stevenchadburrow/Neon6502/Neo6502-Simulator.c

// Neo6502-Simulator.c

// To compile:  gcc -o Neo6502-Simulator.o Neo6502-Simulator.c -lglfw -lGL

// Simulates code for the Neo6502

#include <stdio.h>
#include <stdlib.h>
#include <time.h>

// uses OpenGL for graphics and keyboard
#include <GLFW/glfw3.h>
#include <GL/gl.h>

GLFWwindow* window;
int opengl_window_x = 640;
int opengl_window_y = 480;
int opengl_keyboard_state[512];


unsigned char mandelbrot[80*240] = {

0x55, 0x55, 0x55, 0x55, 0x55, 0x55, 0x55, 0x55, 0x55, 0x55, 0x55, 0x55, 0x55, 0x7F, 0xFE, 0xB2, 
0xA1, 0x55, 0xD5, 0x55, 0x15, 0x29, 0x1C, 0xAA, 0xA0, 0x08, 0xAA, 0xAA, 0xA0, 0x52, 0xA2, 0xAA, 
0x20, 0x28, 0xFF, 0xFF, 0xFF, 0xFF, 0xFF, 0xE2, 0xF0, 0xA0, 0x55, 0x55, 0x55, 0x54, 0x0A, 0xAA, 
0x2A, 0xAA, 0x0A, 0xAA, 0xAA, 0xAA, 0xA8, 0x0A, 0x1A, 0x2A, 0xFC, 0xF5, 0x55, 0x55, 0x55, 0x55, 
0x55, 0x55, 0x55, 0x55, 0x55, 0x55, 0x55, 0x55, 0x55, 0x55, 0x55, 0x55, 0x55, 0x55, 0x55, 0x55, 

0x55, 0x55, 0x55, 0x55, 0x55, 0x55, 0x55, 0x55, 0x55, 0x55, 0x55, 0x55, 0x55, 0x7F, 0xFC, 0xA2, 
0x85, 0x5F, 0xFD, 0x55, 0x42, 0x88, 0x16, 0xAA, 0xAA, 0xA8, 0x2A, 0xA2, 0x21, 0x54, 0xA2, 0xAA, 
0xA8, 0x2A, 0xBF, 0xFF, 0xFF, 0xFF, 0xFF, 0xFE, 0xE2, 0x80, 0x55, 0x55, 0x55, 0x42, 0x8A, 0xAA, 
0xEA, 0xAA, 0x8A, 0xAA, 0xAA, 0xA2, 0xA0, 0x6A, 0x2A, 0x2F, 0xC8, 0xF5, 0x55, 0x55, 0x55, 0x55, 
0x55, 0x55, 0x55, 0x55, 0x55, 0x55, 0x55, 0x55, 0x55, 0x55, 0x55, 0x55, 0x55, 0x55, 0x55, 0x55, 

0x55, 0x55, 0x55, 0x55, 0x55, 0x55, 0x55, 0x55, 0x55, 0x55, 0x55, 0x55, 0x55, 0x7F, 0x3E, 0xA8, 
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
0x80, 0x55, 0x55, 0x55, 0x44, 0x8A, 0xA2, 0xFF, 0xFF, 0xFF, 0xFF, 0xFF, 0xFF, 0xFB, 0xEA, 0xAA, 
0x0A, 0x0F, 0x87, 0xD2, 0xA4, 0x88, 0xAA, 0xAA, 0xAA, 0xAA, 0x00, 0xAA, 0x15, 0x55, 0x7E, 0x2D, 
0x54, 0x0A, 0xBF, 0xAF, 0x55, 0x55, 0x55, 0x55, 0x55, 0x55, 0x55, 0x55, 0x55, 0x55, 0x55, 0x55, 

0x55, 0x55, 0x55, 0x55, 0x55, 0x55, 0x55, 0x55, 0x55, 0x55, 0x55, 0x55, 0x55, 0x55, 0x55, 0x55, 
0x55, 0x5F, 0xAE, 0xBE, 0xAA, 0x88, 0x40, 0xA0, 0x8A, 0xAA, 0xAA, 0x2F, 0xAA, 0xA4, 0x82, 0xA8, 
0xA4, 0x55, 0x55, 0x55, 0x50, 0x0A, 0x8E, 0xBF, 0xFF, 0xFF, 0xFF, 0xFF, 0xFF, 0xFA, 0x8A, 0x22, 
0xAA, 0xAA, 0x87, 0x50, 0xA8, 0x88, 0x2A, 0xAA, 0xAA, 0xAA, 0x80, 0x02, 0x95, 0x55, 0x7F, 0xBD, 
0x54, 0xAA, 0xA3, 0xFB, 0xD5, 0x55, 0x55, 0x55, 0x55, 0x55, 0x55, 0x55, 0x55, 0x55, 0x55, 0x55, 


};



unsigned char cpu_memory[0x10000]; // 64KB of addressable space

unsigned long cpu_reg_a = 0x0000, cpu_reg_x = 0x0000, cpu_reg_y = 0x0000, cpu_reg_s = 0x00FD;
unsigned long cpu_flag_c = 0x0000, cpu_flag_z = 0x0000, cpu_flag_v = 0x0000, cpu_flag_n = 0x0000;
unsigned long cpu_flag_d = 0x0000, cpu_flag_b = 0x0000, cpu_flag_i = 0x0001; // needs to be 0x0001
unsigned long cpu_reg_pc = 0xFFFC;

unsigned long cpu_opcode = 0x0000, cpu_value = 0x0000, cpu_address = 0x0000; 
unsigned long cpu_result = 0x0000, cpu_cycles = 0x0000;

unsigned char cpu_read(unsigned long addr)
{
	return cpu_memory[addr];
}

void cpu_write(unsigned long addr, unsigned char val)
{
	if (addr < 0x8000)
	{
		cpu_memory[addr] = val;
	}
}

// cpu addressing modes
#define CPU_IMM { \
	cpu_value = (unsigned long)cpu_read(cpu_reg_pc++); }

#define CPU_ZPR { \
	cpu_value = (unsigned long)(cpu_memory[(unsigned long)cpu_read(cpu_reg_pc++)]&0x00FF); }

#define CPU_ZPW { \
	cpu_address = (unsigned long)cpu_read(cpu_reg_pc++); }

#define CPU_ZPM { \
	cpu_address = (unsigned long)cpu_read(cpu_reg_pc++); }

#define CPU_ZPXR { \
	cpu_value = (unsigned long)(cpu_memory[(((unsigned long)cpu_read(cpu_reg_pc++)+cpu_reg_x)&0x00FF)]&0x00FF); }

#define CPU_ZPXW { \
	cpu_address = (((unsigned long)cpu_read(cpu_reg_pc++)+cpu_reg_x)&0x00FF); }

#define CPU_ZPXM { \
	cpu_address = (((unsigned long)cpu_read(cpu_reg_pc++)+cpu_reg_x)&0x00FF); }

#define CPU_ZPYR { \
	cpu_value = (unsigned long)(cpu_memory[(((unsigned long)cpu_read(cpu_reg_pc++)+cpu_reg_y)&0x00FF)]&0x00FF); }

#define CPU_ZPYW { \
	cpu_address = (((unsigned long)cpu_read(cpu_reg_pc++)+cpu_reg_y)&0x00FF); }

#define CPU_ABSR { \
	cpu_address = (unsigned long)cpu_read(cpu_reg_pc++); \
	cpu_address += ((unsigned long)cpu_read(cpu_reg_pc++)<<8); \
	cpu_value = (unsigned long)cpu_read(cpu_address); }

#define CPU_ABSW { \
	cpu_address = (unsigned long)cpu_read(cpu_reg_pc++); \
	cpu_address += ((unsigned long)cpu_read(cpu_reg_pc++)<<8); }
	
#define CPU_ABSM { \
	cpu_address = (unsigned long)cpu_read(cpu_reg_pc++); \
	cpu_address += ((unsigned long)cpu_read(cpu_reg_pc++)<<8); }

#define CPU_ABXR { \
	cpu_address = (unsigned long)cpu_read(cpu_reg_pc++); \
	cpu_cycles += ((cpu_address+cpu_reg_x)>>8); \
	cpu_address += ((unsigned long)cpu_read(cpu_reg_pc++)<<8); \
	cpu_address += cpu_reg_x; \
	cpu_value = (unsigned long)cpu_read(cpu_address); }

#define CPU_ABXW { \
	cpu_address = (unsigned long)cpu_read(cpu_reg_pc++); \
	cpu_cycles += ((cpu_address+cpu_reg_x)>>8); \
	cpu_address += ((unsigned long)cpu_read(cpu_reg_pc++)<<8); \
	cpu_address += cpu_reg_x; }
	
#define CPU_ABXM { \
	cpu_address = (unsigned long)cpu_read(cpu_reg_pc++); \
	cpu_address += ((unsigned long)cpu_read(cpu_reg_pc++)<<8); \
	cpu_address += cpu_reg_x; }
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
